Sven65/faderflow/firmware/FaderFlow/src/config.h

//
// Created by Mackan on 2026-02-13.
//

#ifndef FADERFLOW_CONFIG_H
#define FADERFLOW_CONFIG_H

//#define SHARED_MOSI_PIN 11
//#define SHARED_SCLK_PIN 13

#define SHARED_MOSI_PIN 51
#define SHARED_SCLK_PIN 52

#endif //FADERFLOW_CONFIG_H
